backtail/vcadsr-3310/LTSpice_Simulation/CV Inputs.asc

R1: res; 4k7
R2: res; 100k
R3: res; 490k
R4: res; 10k
R5: res; 140k
R6: res; {R}
R7: res; 58k5
U2: ADTL082
V1: voltage; -12
V2: voltage; SINE(0 5 3)
V3: voltage; 12
Named nets: 0, VCC, VEE, CV
.tran 1
Lin A 10k Poti
To Attack, Decay and Release Pin
0V to 5V
.step param R 1m 100k 3k
To Sustain
-5V to 5V
Attack
Release
Decay
Lin A 100k Poti
Sustain
